schneider42/moodlamp-rf/board/bot.png

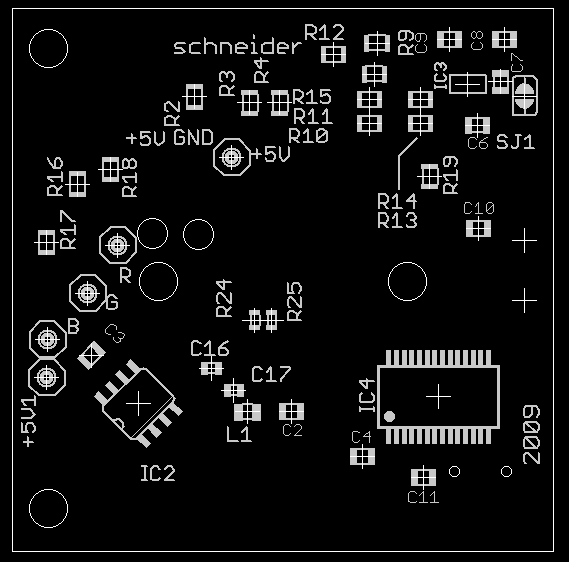
board/bot.png
