schneider42/moodlamp-rf/board/brd.png

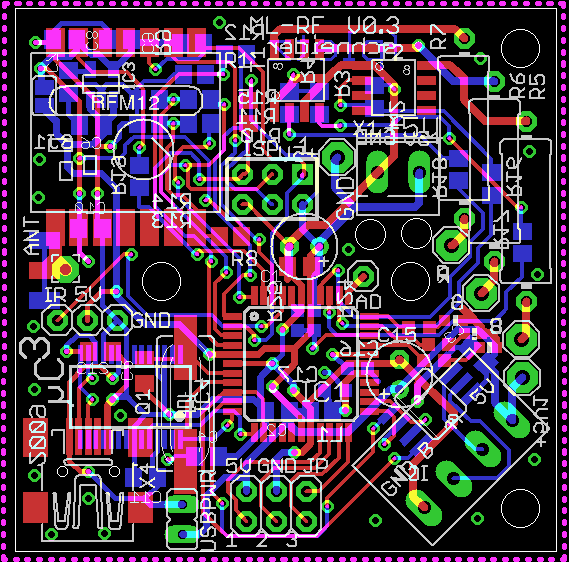
board/brd.png
