schneider42/moodlamp-rf/board/buslamp-sch.png

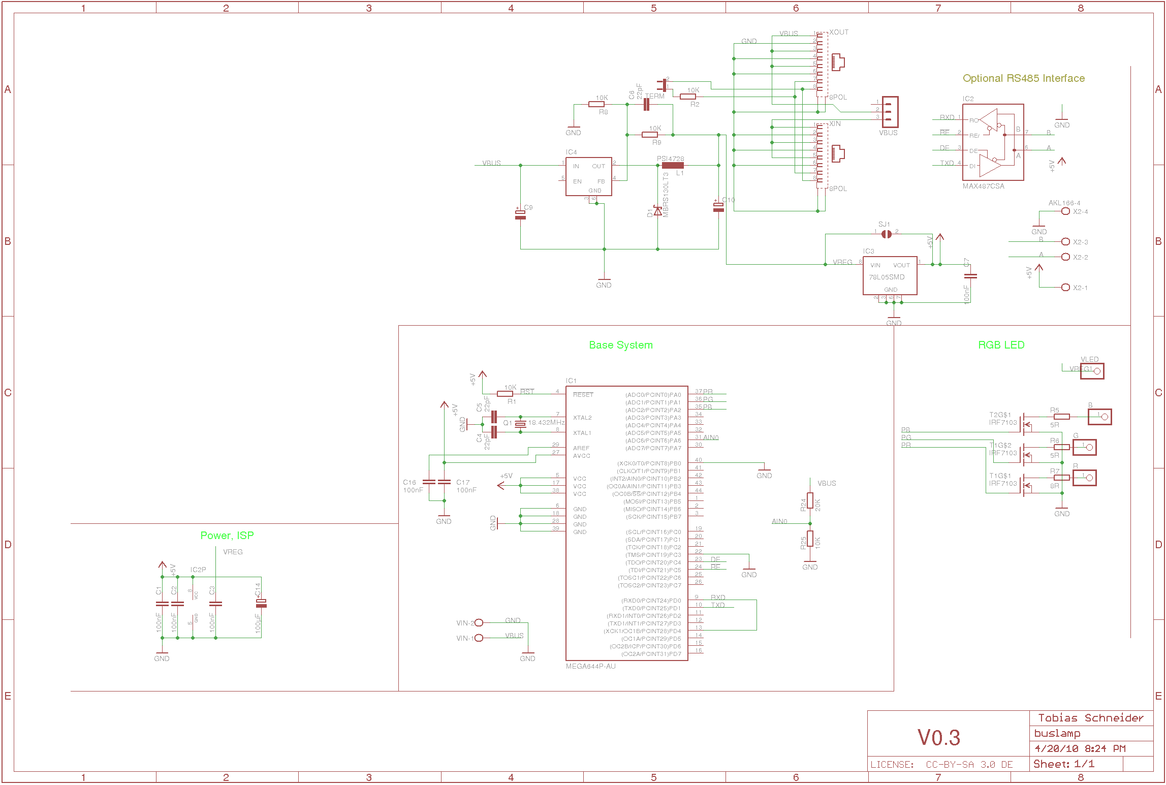
board/buslamp-sch.png
