schneider42/moodlamp-rf/board/qr.png

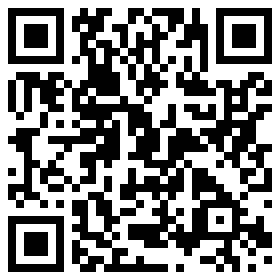
board/qr.png
