schneider42/moodlamp-rf/board/sch.png

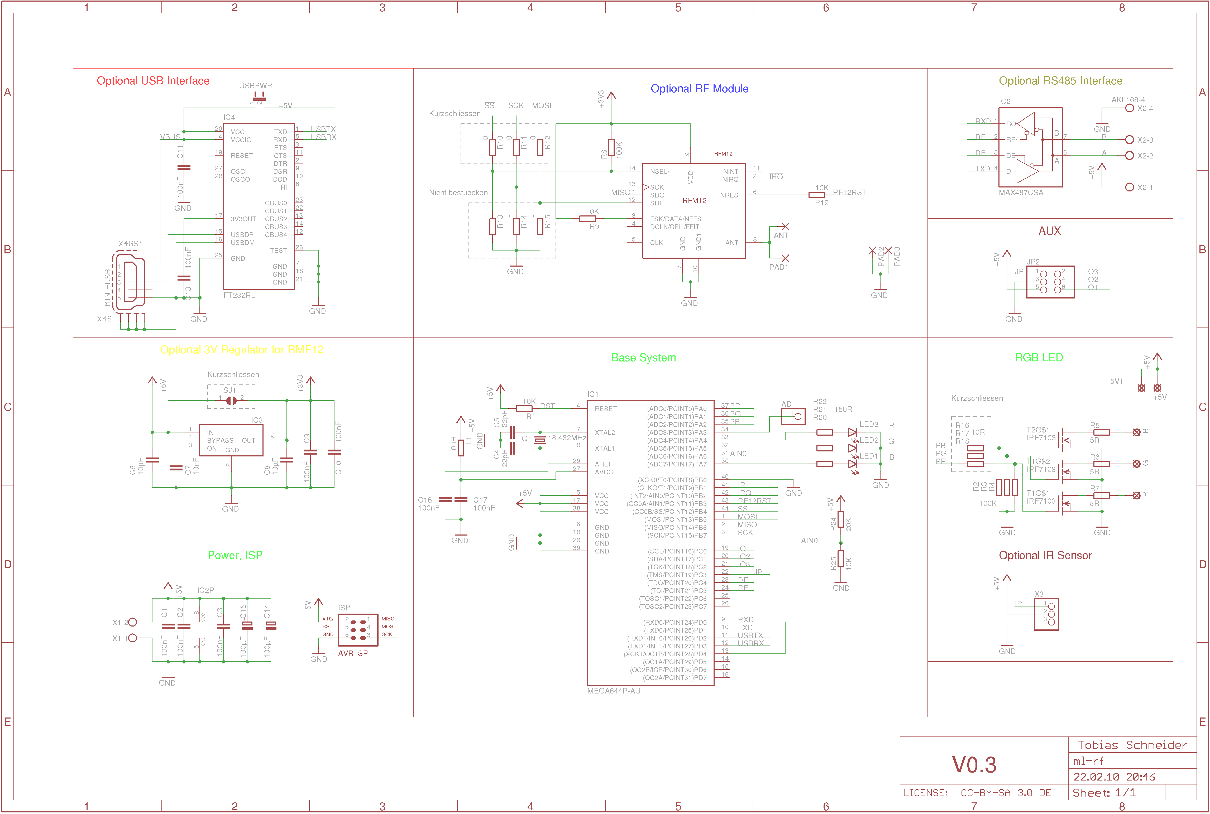
board/sch.png
