schneider42/moodlamp-rf/board/flatlamp/ledboard-r2/ledboard-r2.brd

## EAGLE design board/flatlamp/ledboard-r2/ledboard-r2.brd (2012-12-16)

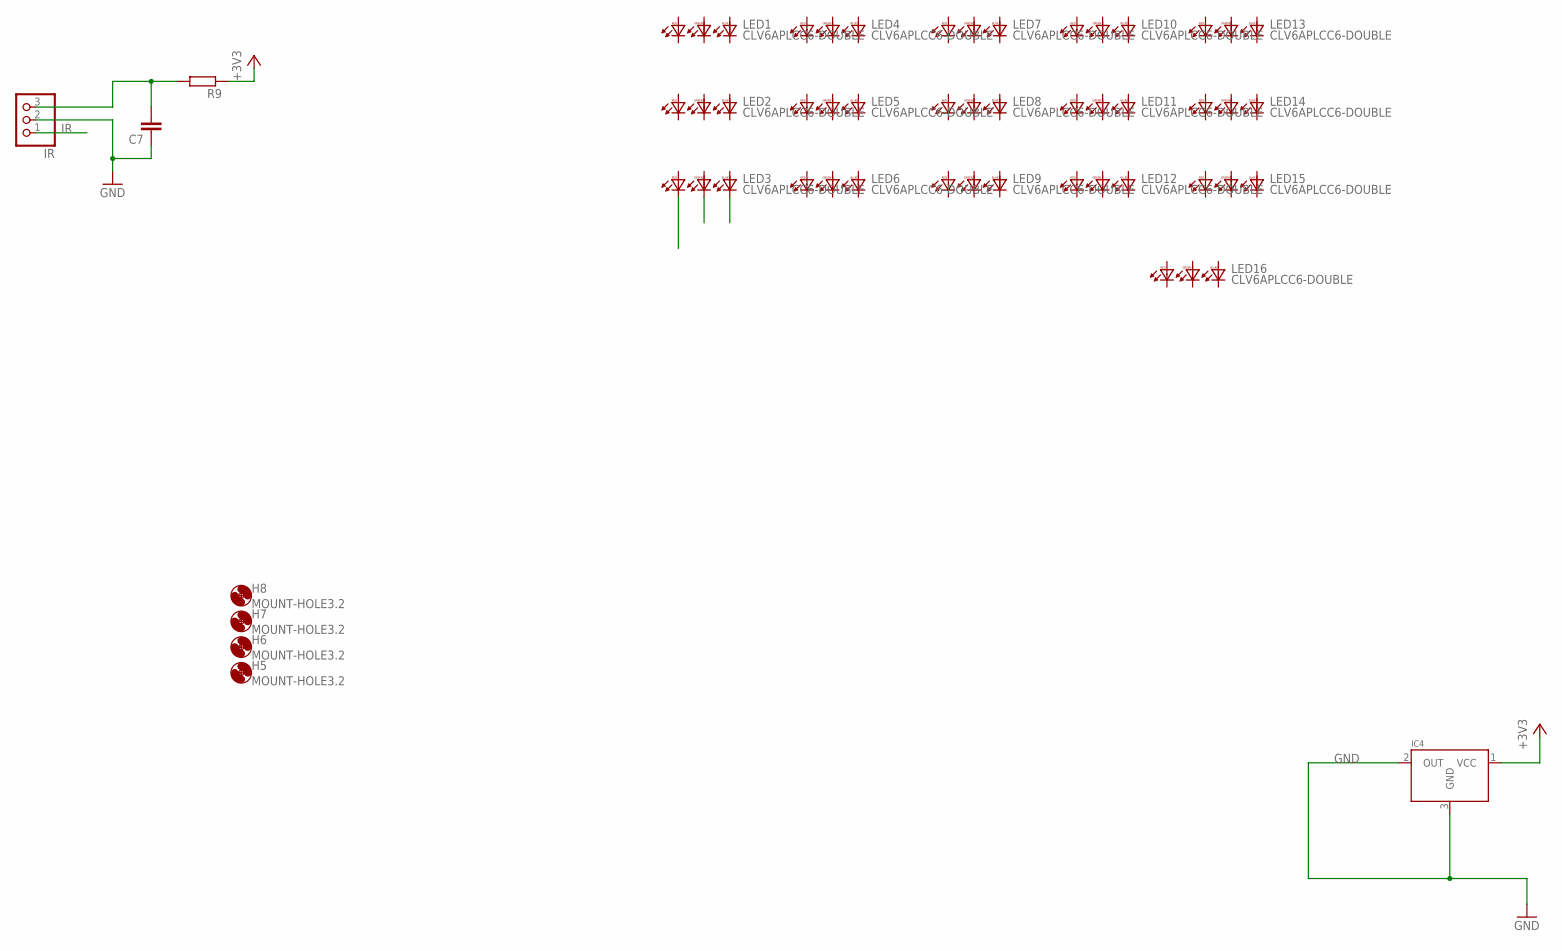
[picture p33: schematic ledboard-r2.sch]

Parts:
C7: C-EUC0805; C0805
H5, H6, H7, H8: MOUNT-HOLE3.2; 3,2
IC4: MCP9701T-E/TTCTREFLOW; SOT23-R
IR: PINHD-1X3; 1X03
LED1, LED2, LED3, LED4, LED5, LED6, LED7, LED8, LED9, LED10, LED11, LED12, LED13, LED14, LED15, LED16: CLV6APLCC6-DOUBLE; PLCC6-DOUBLE
R9: R-EU_R0805; R0805

Connections:
+3V3: IC4.1 (VCC), R9.1
GND: C7.1, IC4.2 (OUT), IC4.3 (GND), IR.2
IR: IR.1
unnamed: C7.2, IR.3, R9.2

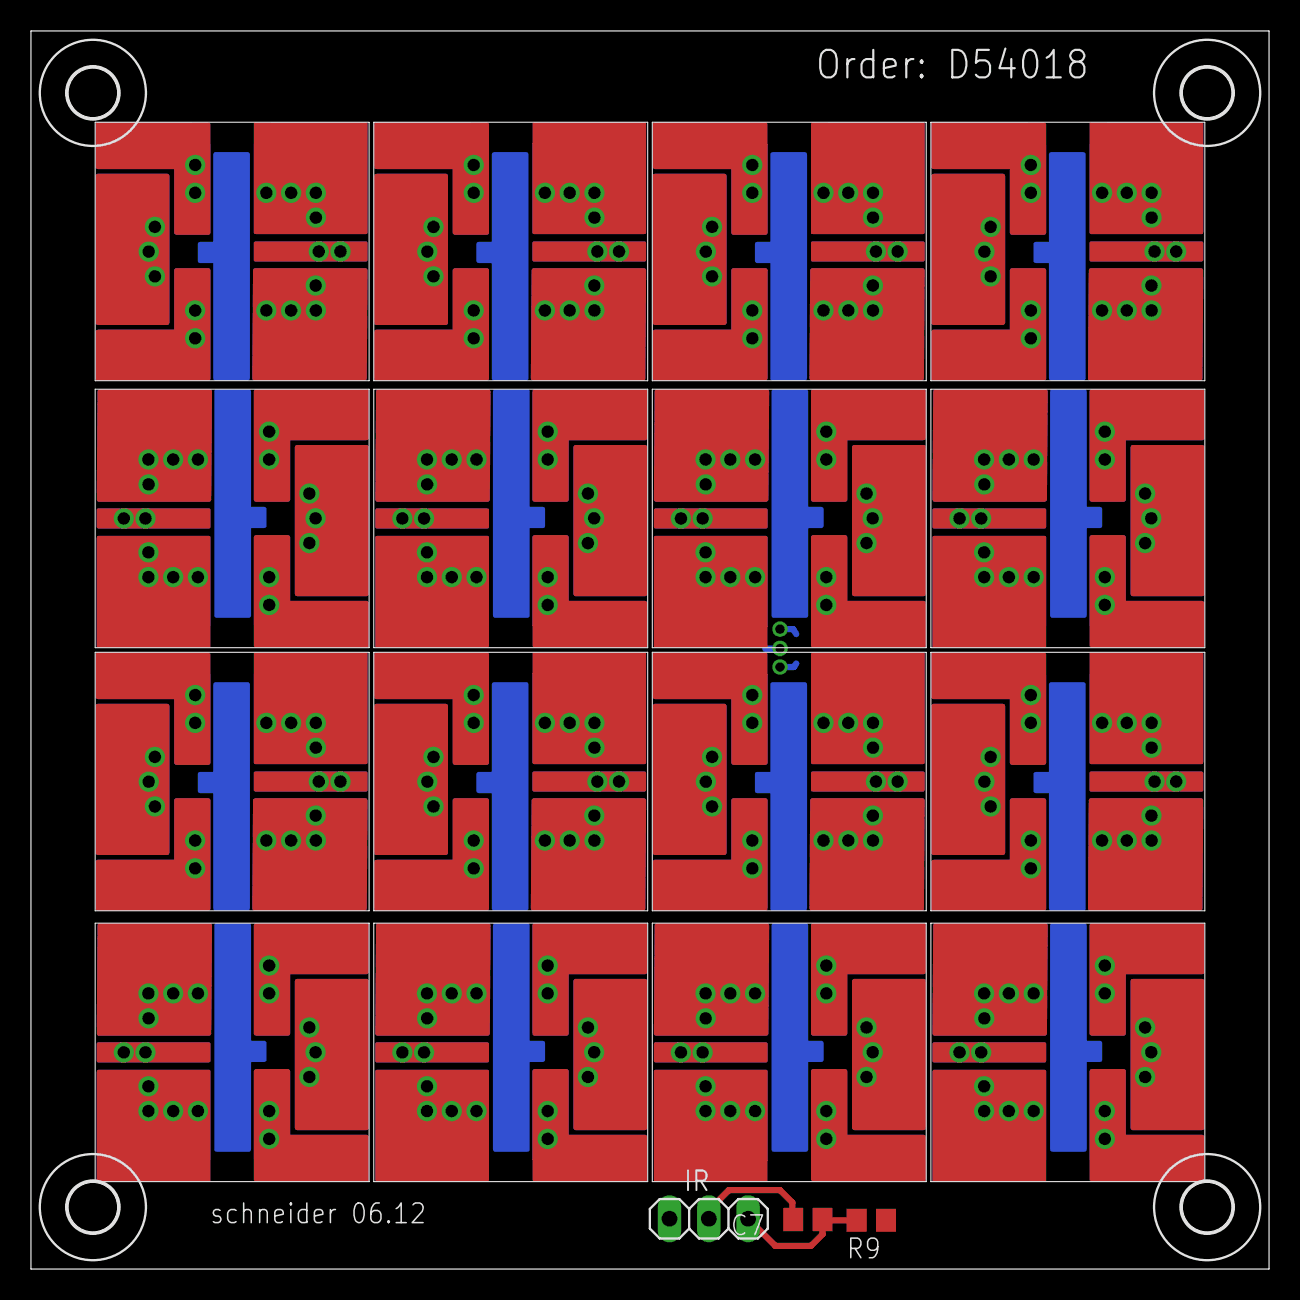
[picture p34: board ledboard-r2.brd from above]

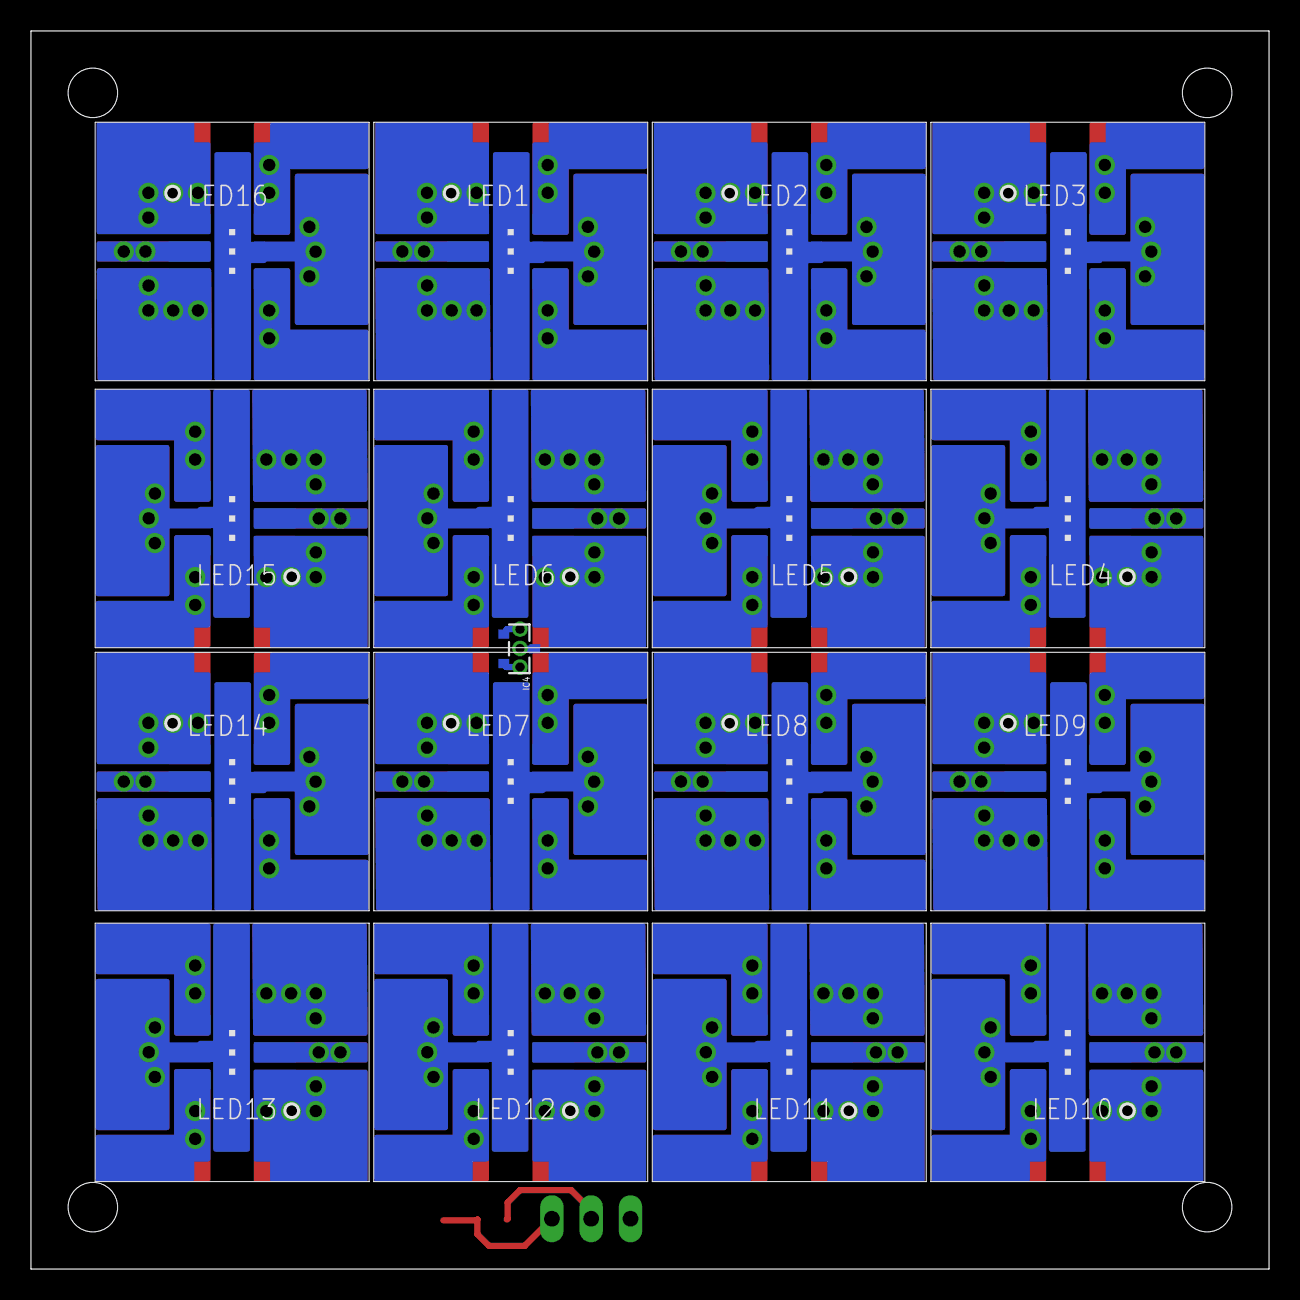
[picture p35: board ledboard-r2.brd from below]

Board: 2 copper layers, 80.0 x 80.0 mm, 24 parts (17 on the bottom side), 3 nets.
