schneider42/moodlamp-rf/moodlamp-bus/fnordlicht.c

/* vim:fdm=marker ts=4 et ai
 * {{{
 *         moodlamp-rf - fnordlicht firmware next generation
 *
 *    for additional information please
 *    see http://blinkenlichts.net/
 *    and http://koeln.ccc.de/prozesse/running/fnordlicht
 *
 * This is a modified version of the fnordlicht
 * (c) by Alexander Neumann <alexander@bumpern.de>
 *     Lars Noschinski <lars@public.noschinski.de>
 *
 * Modifications done by:
 * Kiu
 * Mazzoo
 * Tobias Schneider(schneider@blinkenlichts.net)
 *
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
 * For more information on the GPL, please go to:
 * http://www.gnu.org/copyleft/gpl.html
 }}} */

/* includes */
#include "config.h"

#include <avr/io.h>
#include <stdint.h>
#include <stdlib.h>
#include <avr/interrupt.h>
#include <avr/pgmspace.h>
#include <stdio.h>
#include <string.h>
#include <avr/wdt.h>

#include "common.h"
#include "fnordlicht.h"
#include "pwm.h"
#include "lib/uart.h"

#include "rs485_handler.h"
#include "raw.h"
#include "cmd_handler.h"
#include "control.h"
#if RC5_DECODER
#include "rc5.h"
#endif
#if STATIC_SCRIPTS
#include "static_scripts.h"
#endif
#include "settings.h"
#include "control.h"
#include "packet.h"
#include "pinutils.h"
#include "adc.h"
#include "scripts.h"
#include "leds.h"

#if SERIAL_UART
int uart_putc_file(char c, FILE *stream);
static FILE mystdout = FDEV_SETUP_STREAM(uart_putc_file, NULL, _FDEV_SETUP_WRITE);
#endif

/* structs */
volatile struct global_t global = {{0, 0}};
/* prototypes */
uint16_t main_reset = 0;


#if SERIAL_UART
int uart_putc_file(char c, FILE *stream)
{
    uart1_putc(c);    
    return 0;
}
#endif

void jump_to_bootloader(void)
{
    //uart1_puts("acDRab");
    //cli();
    //wdt_enable(WDTO_30MS);
    while(1);
}

int getxval(int x)
{ 
    int v = toupper(x) - '0';
    if( v < 10 )
        return v;
    return v - 7;
}

unsigned int random_seed __attribute__ ((section (".noinit")));

/** main function
 */
int main(void) {
//    SPCR &= ~(1<<SPE);
//    TIMSK0 &= ~(1<<TOIE1);
    wdt_disable();
    /* Clear WDRF in MCUSR */
    MCUSR &= ~(1<<WDRF);
    /* Write logical one to WDCE and WDE */
    /* Keep old prescaler setting to prevent unintentional time-out */
    WDTCSR |= (1<<WDCE) | (1<<WDE);
    /* Turn off WDT */
    WDTCSR = 0x00;

    DDR_CONFIG_IN(CONFIG1);
    PIN_SET(CONFIG1);
    wdt_enable(WDTO_2S);
    wdt_reset();
    volatile unsigned long l;     
    for(l=0;l<10;l++);

    if( !PIN_HIGH(CONFIG1) ){
        global.config = 30;
    }else{
        global.config = 21;
    }
    
    leds_init();

    wdt_reset();
    if( global.config == 21 ){
        DDR_CONFIG_IN(JUMPER1C1);
        PIN_SET(JUMPER1C1);
    }else if( global.config == 30 ){
        DDR_CONFIG_IN(JUMPER1C2);
        PIN_SET(JUMPER1C2);
        adc_init();
        uint16_t bat = adc_getChannel(6);
        if( bat < ADC_MINBATIDLE ){
            //global.flags.lowbat = 1;
        }
    }
    
    wdt_reset();
    init_pwm();
    global_pwm.channels[0].target_brightness = 255;
    global_pwm.channels[1].target_brightness = 255;

#if SERIAL_UART
    uart1_init( UART_BAUD_SELECT(UART_BAUDRATE,F_CPU));
    stdout = &mystdout;
#endif

#if RC5_DECODER
    rc5_init();
#endif

    wdt_reset();
#if STATIC_SCRIPTS
    init_script_threads();
#endif
    settings_read();
    //if((global.config == 21 && !PIN_HIGH(JUMPER1C1)) || (global.config== 30 && !PIN_HIGH(JUMPER1C2)))
    //    interfaces_setEnabled(IFACE_RF,0);

    control_init();

    wdt_reset();
#if RS485_CTRL
    rs485_init();
    zbus_core_init();
#endif
    int adr = getxval(idbuf[4])*16 + getxval(idbuf[5]);
    
    packet_init(adr,0);

    wdt_reset();
    srandom(random_seed);
    random_seed = random();

    /* enable interrupts globally */
    sei();
//    global.state = STATE_RUNNING;
//    global.state = STATE_PAUSE;
//    global.flags.running = 0;
    while (1) {
        wdt_reset();
        //leds_main();

        #if 1
        packet_tick();
        #else
        if(packetbase ){//> 32){
            packetbase = 0;

            packet_tick();
            //if(main_reset++ > 16000)
            //    jump_to_bootloader(); 
            //uint16_t bat = adc_getChannel(6);
            /*if( bat < ADC_MINBATIDLE ){
                global.flags.lowbat = 1;
            }*/
        }
        #endif
        //if( global.flags.lowbat ){
        //    control_lowbat();
        //}

        if( global.flags.timebase ){
            //control_tick();
            global.flags.timebase=0;
        }
        /* after the last pwm timeslot, rebuild the timeslot table */
        
        //if (global.flags.last_pulse) {
        //    global.flags.last_pulse = 0;
            //if(global.flags.running)
            //update_pwm_timeslots();
        //}
        /* at the beginning of each pwm cycle, call the fading engine and
         * execute all script threads */
        if (global.flags.new_cycle) {
            global.flags.new_cycle = 0;
            if(control_faderunning)
                update_brightness();

            if(global.flags.running){
#if STATIC_SCRIPTS
//                execute_script_threads();
#endif
            }
            //continue;
        }
#if RC5_DECODER
#endif
#if RS485_CTRL
        rs485_process();
#endif
#if SERIAL_UART
//serial_process();
#endif
    }
}
