schneider42/moodlamp-rf/moodlamp-bus/settings.c

/* vim:fdm=marker ts=4 et ai
 * {{{
 *         moodlamp-ng - fnordlicht firmware next generation
 *
 *    for additional information please
 *    see http://blinkenlichts.net/
 *    and http://koeln.ccc.de/prozesse/running/fnordlicht
 *
 * This is a modified version of the fnordlicht
 * (c) by Alexander Neumann <alexander@bumpern.de>
 *     Lars Noschinski <lars@public.noschinski.de>
 *
 * Modifications done by Tobias Schneider(schneider@blinkenlichts.net)
 *
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
 * For more information on the GPL, please go to:
 * http://www.gnu.org/copyleft/gpl.html
 }}} */
#include <avr/eeprom.h>
#include <string.h>

#include "fnordlicht.h"
#include "settings.h"
#include "scripts.h"
#include "static_scripts.h"
#include "pwm.h"
#include "control.h"

struct settings_record_t global_settings_record EEMEM = {1,1};
struct global_pwm_t global_pwm_record EEMEM;
#if STATIC_SCRIPTS
struct thread_t script_threads_record[MAX_THREADS] EEMEM;
#endif
struct timeslots_t pwm_record EEMEM;
struct global_t global_record EEMEM;
struct settings_record_t global_settings;
//char name[50] EEMEM = "\x33master5.lamp.blinkenlichts.net";
char * name = (char *)(E2END - 50);

uint8_t idbuf[60];

void settings_readid(uint8_t * buf)
{
//    eeprom_read_block(buf,&id,sizeof(id));
    eeprom_read_block(buf,name,50);
}

uint8_t settings_compareid(uint8_t * buf)
{
    if(strcmp((char*)idbuf,(char*)buf) == 0)
        return 1;

    return 0;
}

void settings_setid(uint8_t * buf)
{
    return;
    uint8_t len = strlen((char*)buf);
//    if(len > (sizeof(id)-1)){
//        len = sizeof(id)-1;
    if(len > 50){
        len = 49;
        buf[len] = 0;
    }
//    eeprom_write_block(&id,buf,len+1);
  eeprom_write_block(buf,name,len+1);  
}

void settings_save(void)
{
    return;
    const void * temp;
    global_settings.firstboot = 0;
    eeprom_write_block(&global_settings, &global_settings_record,sizeof(global_settings)); 
    temp =(const void *) &global_pwm;       //Just to avoid compiler warnings
    eeprom_write_block(
            temp,
            &global_pwm_record,
            sizeof(global_pwm)
    );
#if STATIC_SCRIPTS
    eeprom_write_block(script_threads,&script_threads_record,sizeof(script_threads)*MAX_THREADS);
#endif
    eeprom_write_block(&pwm,&pwm_record,sizeof(pwm));
    temp = (const void *) &global;
    eeprom_write_block(/*(struct global_t *)&global*/temp,&global_record,sizeof(global));

}

void settings_read(void)
{
    void * temp;
    //eeprom_read_block(&global_settings, &global_settings_record,sizeof(global_settings));
//    if(global_settings.firstboot){
        global_pwm.dim = 255;
#if STATIC_SCRIPTS
//#if RS485_CTRL == 0
        script_threads[0].speed_adjustment = 0;
        script_threads[0].handler.execute = &memory_handler_flash;
        script_threads[0].handler.position = (uint16_t)(&colorchange_red);
        script_threads[0].flags.disabled = 0;

        //script_threads[2].handler.execute = &memory_handler_eeprom;
        //script_threads[2].handler.position = (uint16_t) &testscript_eeprom;
        //script_threads[2].flags.disabled = 0;
//#endif
#endif
        //global_pwm.channels[0].brightness = 250;
        //global_pwm.channels[0].target_brightness = 250;
        global.flags.running = 1;
        global.state = STATE_RUNNING;
        //global.flags.rawmode = 0;
#if 0
    }else{
        temp = (void *) &global_pwm;
        eeprom_read_block(/*(void *)&global_pwm*/temp,&global_pwm_record,sizeof(global_pwm));
#if STATIC_SCRIPTS
        eeprom_read_block(script_threads,&script_threads_record,sizeof(script_threads)*MAX_THREADS);
#endif
        eeprom_read_block(&pwm,&pwm_record,sizeof(pwm));
        temp = (void *) &global;
        eeprom_read_block(/*(struct global_t *)&global*/temp,&global_record,sizeof(global));
    }
#endif
    eeprom_read_block(idbuf,name,50);
#if 0
    if(idbuf[0] == 255){
        strcpy((char*)idbuf,"newlamp.local");
        eeprom_write_block(idbuf,name,50);
    }
#endif

//    eeprom_read_block(idbuf,&id,sizeof(id));
}
