schneider42/moodlamp-rf/dreic/config.h

#ifndef __CONFIG_H_
#define __CONFIG_H_

#define ZBUS_BAUDRATE       115200
#define RS485_CTRL          1

#define RS485_TX_PIN_PORT   C
#define RS485_TX_PIN_PIN    PC4

#define RS485_NRX_PIN_PORT  C
#define RS485_NRX_PIN_PIN   PC5



#endif
