schneider42/moodlamp-rf/moodlamp-bus/cmd_handler.c

/* vim:fdm=marker ts=4 et ai
 * {{{
 *         moodlamp-ng - fnordlicht firmware next generation
 *
 *    for additional information please
 *    see http://blinkenlichts.net/
 *    and http://koeln.ccc.de/prozesse/running/fnordlicht
 *
 * This is a modified version of the fnordlicht
 * (c) by Alexander Neumann <alexander@bumpern.de>
 *     Lars Noschinski <lars@public.noschinski.de>
 *
 * Modifications done by Tobias Schneider(schneider@blinkenlichts.net)
 *
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
 * For more information on the GPL, please go to:
 * http://www.gnu.org/copyleft/gpl.html
 }}} */

#include "config.h"

#include <avr/io.h>
#include <avr/pgmspace.h>
#include <avr/interrupt.h>
#include <string.h>
#include <stdio.h>

#include "common.h"
#include "fnordlicht.h"
#include "pwm.h"
#include "cmd_handler.h"

#if STATIC_SCRIPTS
#include "static_scripts.h"
#include "scripts.h"
#endif
#include "settings.h"
#include "control.h"
#include "packet.h"
#include "adc.h"

void cmd_dark(void)
{
    global_pwm.channels[0].brightness =
                global_pwm.channels[0].target_brightness = 0;
    global_pwm.channels[1].brightness =
                global_pwm.channels[1].target_brightness = 0;
    global_pwm.channels[2].brightness =
                global_pwm.channels[2].target_brightness = 0;
}


void cmd_setscript(void (*execute)(struct thread_t *current_thread), uint16_t position)
{
    script_threads[0].handler.execute = execute;
    script_threads[0].handler.position = position;
    script_threads[0].flags.disabled = 0;
    script_threads[0].handler_stack_offset = 0;
    cmd_dark(); 
}

uint8_t cmd_interpret(uint8_t * cmd, uint8_t * result)
{
    return cmd_handler(cmd[0],cmd+1,result);
}

uint8_t cmd_handler(uint8_t cmd, uint8_t * param, uint8_t * result)
{
   if(cmd == CMD_BRIGHTNESS_DOWN){
        if(global_pwm.dim > 0){
            global_pwm.dim--;
        }
    }else if(cmd == CMD_BRIGHTNESS_UP){
        if(global_pwm.dim < 255){
            global_pwm.dim++;
        }
    }else if(cmd == CMD_FULL_BRIGHTNESS){
        global_pwm.dim=255;
    }else if(cmd == CMD_ZERO_BRIGHTNESS){
        global_pwm.dim=0;
    }else if(cmd == CMD_POWER){
        if(global.state != STATE_STANDBY){
            if(global.state == STATE_SLEEP)
                global.oldstate = STATE_RUNNING;
            else
                global.oldstate = global.state;
            //global.state = STATE_ENTERSTANDBY;
            control_standby(0);
        }else{
            global.state = STATE_LEAVESTANDBY;
        }
    }else if(cmd == CMD_SET_SCRIPT){
        if(sizeof(global_playlist)/(sizeof(struct playlist_t)) > param[0])
                cmd_setscript(
                    global_playlist[param[0]].execute, global_playlist[param[0]].position);
    }else if(cmd == CMD_FASTER){
        if(script_threads[0].speed_adjustment < 8){
            script_threads[0].speed_adjustment++;
            respeed(&script_threads[0]);
            //update_brightness();
            //execute_script_threads();
        }

    }else if(cmd == CMD_SLOWER){
        if(script_threads[0].speed_adjustment > -8){
            script_threads[0].speed_adjustment--;
            respeed(&script_threads[0]);
            //update_brightness();
            //execute_script_threads();
        }
    }else if(cmd == CMD_PAUSE){
        if(global.state != STATE_PAUSE)
            global.state = STATE_PAUSE;
        else
            global.state = STATE_RUNNING;
    }else if(cmd == CMD_SAVE){
        settings_save();
    }else if(cmd == CMD_SLEEP){
        global.state = STATE_ENTERSLEEP;
    }else if(cmd == CMD_RED){
        global_pwm.channel_modifier = 0;
    }else if(cmd == CMD_GREEN){
        global_pwm.channel_modifier = 1;
    }else if(cmd == CMD_BLUE){
        global_pwm.channel_modifier = 2;
    }else if(cmd == CMD_COLOR_UP){
        global_pwm.channels[global_pwm.channel_modifier].brightness++;
    }else if(cmd == CMD_COLOR_DOWN){
        global_pwm.channels[global_pwm.channel_modifier].brightness--;
    }else if(cmd == CMD_COLOR_FULL){
        global_pwm.channels[global_pwm.channel_modifier].brightness=255;
    }else if(cmd == CMD_COLOR_ZERO){
        global_pwm.channels[global_pwm.channel_modifier].brightness=0;
    }else if(cmd == CMD_GET_VERSION){
        //strcpy((char *) result,"D=");
        //strcat((char *) result,__DATE__);
        //strcat((char *) result,"H=");

        //strcpy((char *) result, "D="__DATE__"H=");
        //strcat((char *) result,__DATE__);
        //sprintf((char *)result,"D="__DATE__" H=%d",global.config);
        return strlen((char *)result);
    }else if(cmd == CMD_GET_STATE){
        result[0] = global.state;
        result[1] = script_threads[0].speed_adjustment;
        result[2] = global_pwm.dim;
        return 3;
    }else if(cmd == CMD_SET_SPEED){
        script_threads[0].speed_adjustment = param[0]; 
    }else if(cmd == CMD_SET_STATE){
        global.state = param[0];
    }else if(cmd == CMD_SET_BRIGHTNESS){
        global_pwm.dim = param[0];
    }else if(cmd == CMD_SET_COLOR){
        control_setColor(param[0],param[1],param[2]);
    }else if(cmd == CMD_RESET){
        jump_to_bootloader();
    }else if(cmd == CMD_SERVER_SET){
        if(settings_compareid(param)){
            uint8_t pos = strlen((char*)param);
            packet_setAddress(param[pos+1],param[pos+2]);
            control_setServer(param[pos+3]);
        }
    }else if(cmd == CMD_SETUP_OK){
        control_setupOK();
    }else if(cmd == CMD_SET_NAME){
        settings_setid(param);
        settings_readid(result+1);
        return strlen((char*)result);
    }else if(cmd == CMD_RAW){
        if(param[0]){
            global.flags.rawmode = 1;
            //uart1_puts("acDsetrawab");
        }else{
            global.flags.rawmode = 0;
        }
    }else if(cmd == CMD_DISABLE_BEACON){
        control_beacontime = 0;
    }else if(cmd ==  CMD_SELF_ASSIGN){
        control_selfassign();
    }else if(cmd == CMD_STANDALONE){
        control_beacontime = 0;
        control_selfassign();
    }else if(cmd == CMD_FADE){
        uint16_t speed = (param[3]<<8)+param[4];
        control_fade(param[0],param[1],param[2],speed);
    }else if(cmd == CMD_FADEMS){
        uint16_t time = (param[3]<<8)+param[4];
        control_fadems(param[0],param[1],param[2],time);
    }else if(cmd == CMD_FADEMSALT){
        uint16_t time = (param[3]<<8)+param[4];
        control_fademsalt(param[0],param[1],param[2],time);
    }else if(cmd == CMD_GET_VOLTAGE){
        uint16_t adc = adc_getChannel(6);
        //sprintf((char *)result,"V=%u",adc);
        return strlen((char *)result);
    }else if(cmd == CMD_UPDATE){
        control_update();
    }else if(cmd == CMD_PREPARE){
        control_prepareColor(param[0],param[1],param[2]);
    }else if(cmd == CMD_PREPARE_FADE){
        uint16_t speed = (param[3]<<8)+param[4];
        control_prepareFade(param[0],param[1],param[2], speed);
    }else if(cmd == CMD_PREPARE_FADEMS){
        uint16_t time = (param[3]<<8)+param[4];
        control_prepareFadems(param[0],param[1],param[2], time);
    }else if(cmd == CMD_PREPARE_FADEMSALT){
        uint16_t time = (param[3]<<8)+param[4];
        control_prepareFademsalt(param[0],param[1],param[2], time);
    }else if(cmd == CMD_DICE){
        if( (random() & 0xff) < 23 )
            jump_to_bootloader();    
    }
    return 0;
}
