schneider42/moodlamp-rf/rs485bridge/leds.h

#ifndef __LEDS_H_
#define __LEDS_H_
void leds_init(void);
inline void leds_rx(void);
inline void leds_rxend(void);
inline void leds_tx(void);
inline void leds_txend(void);
inline void leds_driveon(void);
inline void leds_driveoff(void);
inline void leds_main(void);
#endif
