schneider42/moodlamp-rf/ubloader/serialinterface.py

import serial
import string
import sys
import time
import crcmod

class SerialInterface:
    def  __init__ ( self, path2device, baudrate, timeout=0):
        self.ser = serial.Serial(path2device, baudrate)
        self.ser.flushInput()
        self.ser.flushOutput()
        if timeout:
            self.ser.setTimeout(timeout)

    def writeMessage(self,message):

        c = crcmod.Crc(0x11021)
        c.update(message);
        message += c.digest()
        #the bootloader needs escaping
        message = message.replace('\\','\\\\')
        enc = "\\5" + message + "\\2"
        data = enc.replace('\\','\\\\')
        #print "writing",list(enc)
        self.ser.write(data)
    def write(self, data):
        #the bridge needs escaping
        data = data.replace('\\','\\\\')
        self.ser.write(data)

    def readMessage(self):
        data = ""
        escaped = False
        stop = False
        start = False

        while True:
            d = ''
            c = self.ser.read(1)
            if len(c) == 0:             #A timout occured
                print 'TIMEOUT'
                return False
            #print "c=", c,list(c)
        #    continue
            if escaped:
                if c == '5':
                    start = True
                    data = ""
                elif c == '2':
                    stop = True
                elif c == '\\':
                    d = '\\'
                escaped = False
            elif c == '\\':
                escaped = 1
            else:
                d = c
                
            if start:
                start = False
            elif stop:
                if data[0] == 'D':
                    #print 'serial debug message: %d %s'%(len(data), data)
                    data = ""
                    stop = False
                else:
                    #print 'received message: len=%d data=%s'%(len(data),data)
                    #print list(data)
                    return data
            elif escaped == False:
                data += str(d)
