schneider42/moodlamp-rf/moodlamp-bus/static_scripts.c

/* vim:fdm=marker ts=4 et ai
 * {{{
 *         moodlamp-ng - fnordlicht firmware next generation
 *
 *    for additional information please
 *    see http://blinkenlichts.net/
 *    and http://koeln.ccc.de/prozesse/running/fnordlicht
 *
 * This is a modified version of the fnordlicht
 * (c) by Alexander Neumann <alexander@bumpern.de>
 *     Lars Noschinski <lars@public.noschinski.de>
 *
 * Modifications done by Tobias Schneider(schneider@blinkenlichts.net)
 *
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
 * For more information on the GPL, please go to:
 * http://www.gnu.org/copyleft/gpl.html
 }}} */
#include "config.h"

#if STATIC_SCRIPTS

#include "static_scripts.h"
#include "pwm.h"
#include <stdint.h>
#include <stdlib.h>
#include <avr/pgmspace.h>


/* local prototypes */
void sleep_handler(struct thread_t *current_thread);
void wait_handler(struct thread_t *current_thread);

/* opcode handlers */
/* {{{ */
uint8_t opcode_handler_rnd_channel(uint8_t parameters[], struct thread_t *current_thread);
uint8_t opcode_handler_fade_channel(uint8_t parameters[], struct thread_t *current_thread);
uint8_t opcode_handler_fade_channels(uint8_t parameters[], struct thread_t *current_thread);
uint8_t opcode_handler_jump(uint8_t parameters[], struct thread_t *current_thread);
uint8_t opcode_handler_set_channel(uint8_t parameters[], struct thread_t *current_thread);
uint8_t opcode_handler_sleep(uint8_t parameters[], struct thread_t *current_thread);
uint8_t opcode_handler_wait(uint8_t parameters[], struct thread_t *current_thread);
uint8_t opcode_handler_clear(uint8_t parameters[], struct thread_t *current_thread);
uint8_t opcode_handler_stop(uint8_t parameters[], struct thread_t *current_thread);
/* }}} */


/* opcode lookup table */
/* {{{ */
uint8_t (*opcode_lookup_table[])(uint8_t parameters[], struct thread_t *current_thread) = {
    &opcode_handler_rnd_channel,    /* opcode 0x00 */
    &opcode_handler_fade_channel,   /* opcode 0x10 */
    &opcode_handler_fade_channels,  /* opcode 0x20 */
    &opcode_handler_jump,           /* opcode 0x30 */
    &opcode_handler_set_channel,    /* opcode 0x40 */
    &opcode_handler_sleep,          /* opcode 0x50 */
    &opcode_handler_wait,           /* opcode 0x60 */
    &opcode_handler_clear,          /* opcode 0x70 */
    &opcode_handler_stop            /* opcode 0x80 */
        };
/* }}} */


/* init all structures in the global array 'script_threads' */
void init_script_threads(void)
/* {{{ */ {
    uint8_t i;

    /* iterate over all threads */
    for (i=0; i<MAX_THREADS; i++) {
        script_threads[i].handler.execute = 0;
        script_threads[i].handler.position = 0;

        script_threads[i].flags.channel_target_reached = 0;
        script_threads[i].flags.disabled = 1;

        script_threads[i].handler_stack_offset = 0;

#if SCRIPT_SPEED_CONTROL
        script_threads[i].speed_adjustment = 0;
#endif
    }
}
/* }}} */

/* iterate over all threads and execute each, if enabled */
void execute_script_threads(void)
/* {{{ */ {
    uint8_t i;
    uint8_t target_mask = 0;

    /* check for channels which reached their targets */
    for (i=0; i<PWM_CHANNELS; i++) {
        if (global_pwm.channels[i].flags.target_reached) {
            target_mask |= global_pwm.channels[i].mask;
            global_pwm.channels[i].flags.target_reached = 0;
        }
    }

    /* iterate over all threads */
    for (i=0; i<MAX_THREADS; i++) {
        /* update channel target reached mask */
        script_threads[i].flags.channel_target_reached |= target_mask;

        /* execute enabled threads */
        if (!script_threads[i].flags.disabled) {
            script_threads[i].handler.execute(&script_threads[i]);
        }
    }
}
/* }}} */

/* memory handlers */
void memory_handler_flash(struct thread_t *current_thread)
/* {{{ */ {
    uint8_t opcode;
    uint8_t parameters[4];
    uint8_t i;

    while (1) {
        /* read opcode and parameters and call the appropiate opcode processing function */
        opcode = pgm_read_byte((current_thread->handler.position)++);
        current_thread->handler.opcode = opcode;
        /* safe flags as first parameter */
        parameters[0] = (opcode & 0x0f);

        /* extract real opcode */
        opcode >>= 4;

        /* load other parameters */
        for (i=1; i<4; i++) {
            parameters[i] = pgm_read_byte((current_thread->handler.position)++);
        }

        /* call opcode handler */
        i = (opcode_lookup_table[opcode])(parameters, current_thread);

        if (i == OP_RETURN_STOP) {
            (*current_thread).flags.disabled = 1;
            break;
        } else if (i == OP_RETURN_BREAK) {
            break;
        }
    }
}
/* }}} */

void memory_handler_eeprom(struct thread_t *current_thread)
/* {{{ */ {
    uint8_t opcode;
    uint8_t parameters[4];
    uint8_t i;

    while (1) {
        /* read opcode and parameters and call the appropiate opcode processing function */
        opcode = eeprom_read_byte((uint8_t *)(current_thread->handler.position)++);
        current_thread->handler.opcode = opcode;
        /* safe flags as first parameter */
        parameters[0] = (opcode & 0x0f);

        /* extract real opcode */
        opcode >>= 4;

        /* load other parameters */
        for (i=1; i<4; i++) {
            parameters[i] = eeprom_read_byte((uint8_t *)(current_thread->handler.position)++);
        }

        /* call opcode handler */
        i = (opcode_lookup_table[opcode])(parameters, current_thread);

        if (i == OP_RETURN_STOP) {
            (*current_thread).flags.disabled = 1;
            break;
        } else if (i == OP_RETURN_BREAK) {
            break;
        }
    }
}
/* }}} */

/* other (module-local) handlers */
void sleep_handler(struct thread_t *current_thread)
/* {{{ */ {
    /* restore old handler, if time is over */
    if ((--current_thread->handler.position) == 0) {
        current_thread->handler_stack_offset--;
        current_thread->handler.execute = current_thread->handler_stack[current_thread->handler_stack_offset].execute;
        current_thread->handler.position = current_thread->handler_stack[current_thread->handler_stack_offset].position;
        current_thread->handler.opcode = 0;
    }

}
/* }}} */

void wait_handler(struct thread_t *current_thread)
/* {{{ */ {
    /* restore old handler and clear target_reached mask, if a channel we wait
     * for has reached it's target */

    if (current_thread->handler.position & current_thread->flags.channel_target_reached) {
        /* clear bitmask */
        current_thread->flags.channel_target_reached &= ~current_thread->handler.position;

        /* restore old handler */
        current_thread->handler_stack_offset--;
        current_thread->handler.execute = current_thread->handler_stack[current_thread->handler_stack_offset].execute;
        current_thread->handler.position = current_thread->handler_stack[current_thread->handler_stack_offset].position;
        current_thread->handler.opcode = 0;
    }

}
/* }}} */


/* opcode handlers */
uint8_t opcode_handler_nop(uint8_t parameters[], struct thread_t *current_thread)
/* {{{ */ {
    /* do exactly nothing */
    (void) parameters;
    (void) current_thread;

    return OP_RETURN_BREAK;
}
/* }}} */

uint8_t opcode_handler_fade_channel(uint8_t parameters[], struct thread_t *current_thread)
/* {{{ */ {
    uint16_t speed = (parameters[3] << 8) + parameters[2];
#if SCRIPT_SPEED_CONTROL
    //global_pwm.channels[parameters[0]].speed_orig = speed;
    global_pwm.speed_orig[parameters[0]] = speed;
    if ((current_thread->speed_adjustment) < 0) {
        speed >>= -current_thread->speed_adjustment;
        if (speed == 0)
            speed = 1;
    } else if (current_thread->speed_adjustment > 0) {
        speed <<= current_thread->speed_adjustment;
        if (speed == 0)
            speed = 0xFFFF;
    }
#else
    (void) current_thread;
#endif

    global_pwm.channels[parameters[0]].target_brightness = parameters[1];
    global_pwm.channels[parameters[0]].speed_l = LOW(speed);
    global_pwm.channels[parameters[0]].speed_h = HIGH(speed);
    
    //current_thread->flags.channel_target_reached &= ~global_pwm.channels[parameters[0]].mask;
    return OP_RETURN_OK;
}
/* }}} */


void respeed(struct thread_t *current_thread)
{
    uint16_t i;
    if((current_thread->handler.opcode & 0xF0) == OP_SLEEP){
        uint16_t speed = current_thread->wait_speed_orig;
        if ((current_thread->speed_adjustment) < 0) {
            speed <<= -current_thread->speed_adjustment;
            if (speed == 0)
                speed = 0xffff;
        } else if (current_thread->speed_adjustment > 0) {
            speed >>= current_thread->speed_adjustment;
            if (speed == 0)
                speed = 1;
            //if (speed < 10)
            //    speed = 10;
        }
        current_thread->handler.position = speed;
        //current_thread->handler.position = current_thread->wait_speed_orig;
    }else// if(current_thread->handler.opcode & OP_FADE_CHANNEL || current_thread->handler.opcode & OP_FADE_CHANNELS 
   // || current_thread->handler.opcode & OP_WAIT)
    {
        for(i=0;i<3;i++){
            //uint16_t speed = global_pwm.channels[i].speed_orig;
            uint16_t speed = global_pwm.speed_orig[i];
            if ((current_thread->speed_adjustment) < 0) {
                speed >>= -current_thread->speed_adjustment;
                if (speed == 0)
                    speed = 1;
            } else if (current_thread->speed_adjustment > 0) {
                speed <<= current_thread->speed_adjustment;
                if (speed == 0)
                    speed = 0xFFFF;
            }
            
            global_pwm.channels[i].speed_l = LOW(speed);
            global_pwm.channels[i].speed_h = HIGH(speed);
            //global_pwm.channels[i].speed = global_pwm.speed_orig[i];
            global_pwm.channels[i].speed = speed;
        }
    }
}

uint8_t opcode_handler_rnd_channel(uint8_t parameters[], struct thread_t *current_thread)
/* {{{ */ {
    (void) current_thread;

    uint8_t r;
    uint8_t channel = parameters[1];

    r = (uint8_t)0xff & (random() + (uint16_t)parameters[2]);       //minimum speed?
    if (!r) r=1;
    global_pwm.channels[channel].speed_l = r;

    r =  random() & 0xff;
    while (r>parameters[3])                                         //maximum speed?
        r >>= 1;
    global_pwm.channels[channel].speed_h = r;

    r = random() & 0xff;
    /* FIXME this is a workaround for a bug in opcode_handler_wait()
     *       when target_brightness equals the old value */
    while (r == global_pwm.channels[channel].target_brightness)
        r = random() & 0xff;

    global_pwm.channels[channel].target_brightness  = r;

    return OP_RETURN_OK;
}
/* }}} */

uint8_t opcode_handler_fade_channels(uint8_t parameters[], struct thread_t *current_thread)
/* {{{ */ {
    (void) current_thread;

    global_pwm.channels[0].target_brightness = parameters[1];
    global_pwm.channels[1].target_brightness = parameters[2];
    global_pwm.channels[2].target_brightness = parameters[3];

    return OP_RETURN_OK;
}
/* }}} */

uint8_t opcode_handler_jump(uint8_t parameters[], struct thread_t *current_thread)
/* {{{ */ {
    int16_t offset = ((int8_t) parameters[1]);

    /* correct offset so that -1 really jumps to the instruction _before_ this one */
    if (offset < 0)
        offset--;

    /* comput the byte offset */
    offset *= 4;

    /* save new offset */
    current_thread->handler.position += offset;

    return OP_RETURN_OK;
}
/* }}} */

uint8_t opcode_handler_set_channel(uint8_t parameters[], struct thread_t *current_thread)
/* {{{ */ {
    (void) current_thread;

    global_pwm.channels[parameters[1]].brightness = parameters[2];
    global_pwm.channels[parameters[1]].target_brightness = parameters[2];

    return OP_RETURN_OK;
}
/* }}} */

uint8_t opcode_handler_sleep(uint8_t parameters[], struct thread_t *current_thread)
/* {{{ */ {
    uint16_t speed = (parameters[2] << 8) + parameters[1];

#if SCRIPT_SPEED_CONTROL
    current_thread->wait_speed_orig = speed;
    if ((current_thread->speed_adjustment) < 0) {
        speed <<= -current_thread->speed_adjustment;
        if (speed == 0)
            speed = 0xffff;
    } else if (current_thread->speed_adjustment > 0) {
        speed >>= current_thread->speed_adjustment;
        if (speed == 0)
            speed = 1;
        //if (speed < 10)
        //    speed = 10;
    }
#endif

    /* save old handler and old position onto the handler stack in the current thread */
    current_thread->handler_stack[current_thread->handler_stack_offset].execute = current_thread->handler.execute;
    current_thread->handler_stack[current_thread->handler_stack_offset].position = current_thread->handler.position;

    current_thread->handler.execute = &sleep_handler;
    current_thread->handler.position = speed;

    current_thread->handler_stack_offset++;

    return OP_RETURN_BREAK;
}
/* }}} */

uint8_t opcode_handler_wait(uint8_t parameters[], struct thread_t *current_thread)
/* {{{ */ {
    /* save old handler and old position onto the handler stack in the current thread */
    current_thread->handler_stack[current_thread->handler_stack_offset].execute = current_thread->handler.execute;
    current_thread->handler_stack[current_thread->handler_stack_offset].position = current_thread->handler.position;

    current_thread->handler.execute = &wait_handler;
    current_thread->handler.position = parameters[1];

    current_thread->handler_stack_offset++;

    return OP_RETURN_BREAK;
}
/* }}} */

uint8_t opcode_handler_clear(uint8_t parameters[], struct thread_t *current_thread)
/* {{{ */ {
    (void) parameters;

    /* clear channel target reached flags for this thread */
    current_thread->flags.channel_target_reached = 0;

    return OP_RETURN_OK;
}
/* }}} */

uint8_t opcode_handler_stop(uint8_t parameters[], struct thread_t *current_thread)
/* {{{ */ {
    (void) current_thread;
    (void) parameters;

    return OP_RETURN_STOP;
}
/* }}} */



#endif
